hssnadr/RGB-Lamp-Demonstrator/images/03.jpg

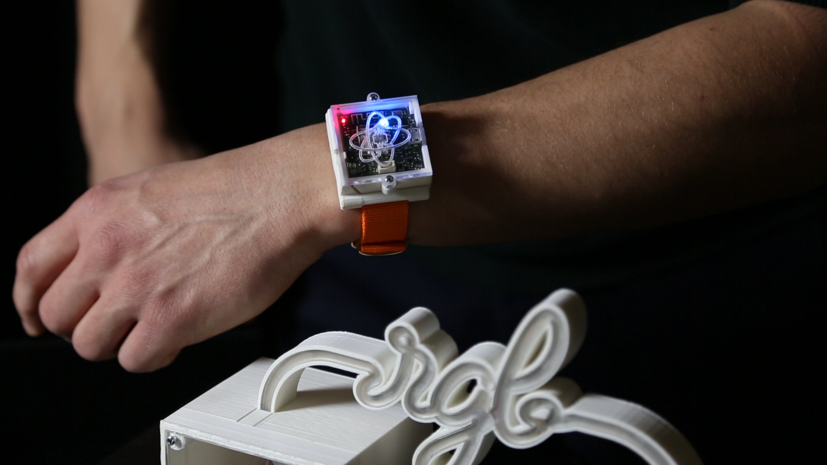
images/03.jpg
