hssnadr/RGB-Lamp-Demonstrator/images/04.jpg

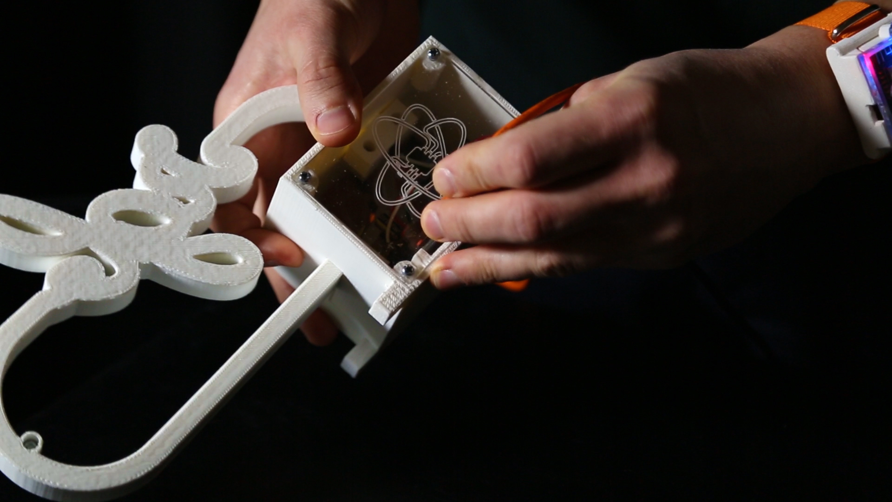
images/04.jpg
